modularev/Nemesis/software/examples/polysynth/include/SourceCodeProItalic14.h

const uint8_t SourceCodePro_ExtraLightItalic14pt7bBitmaps[] PROGMEM = {
  0x04, 0x20, 0x82, 0x08, 0x21, 0x04, 0x10, 0x41, 0x08, 0x00, 0x00, 0x18,
  0xE3, 0x80, 0x61, 0xB0, 0xD8, 0x68, 0x24, 0x12, 0x0A, 0x09, 0x04, 0x02,
  0x10, 0x10, 0x81, 0x04, 0x08, 0x40, 0x42, 0x1F, 0xDC, 0x21, 0x01, 0x08,
  0x10, 0x40, 0x84, 0x04, 0x21, 0xFF, 0xC2, 0x10, 0x10, 0x81, 0x04, 0x08,
  0x40, 0x42, 0x02, 0x10, 0x00, 0x00, 0x80, 0x08, 0x00, 0x80, 0x10, 0x0F,
  0x81, 0x06, 0x20, 0x12, 0x00, 0x20, 0x01, 0x00, 0x08, 0x00, 0x60, 0x01,
  0x80, 0x04, 0x00, 0x20, 0x02, 0x00, 0x28, 0x02, 0x40, 0x43, 0xF8, 0x08,
  0x00, 0x80, 0x08, 0x00, 0x80, 0x18, 0x00, 0x33, 0x00, 0x50, 0x80, 0x50,
  0x40, 0x48, 0x20, 0x44, 0x10, 0x42, 0x08, 0x41, 0x08, 0x00, 0x78, 0x00,
  0x00, 0x0C, 0x00, 0x19, 0x80, 0x88, 0x40, 0x88, 0x20, 0x84, 0x10, 0x82,
  0x08, 0x81, 0x04, 0x80, 0x84, 0x00, 0x3C, 0x00, 0x03, 0xC0, 0x10, 0x80,
  0x42, 0x02, 0x08, 0x08, 0x40, 0x22, 0x00, 0x90, 0x01, 0x80, 0x0C, 0x00,
  0x50, 0x16, 0x20, 0x50, 0x82, 0x81, 0x12, 0x04, 0x48, 0x0A, 0x20, 0x10,
  0x81, 0xA1, 0xF8, 0x60, 0x6D, 0xA4, 0xA4, 0x00, 0xC0, 0x40, 0x20, 0x10,
  0x08, 0x04, 0x02, 0x00, 0x80, 0x40, 0x10, 0x08, 0x02, 0x00, 0x80, 0x20,
  0x08, 0x02, 0x00, 0x80, 0x20, 0x08, 0x01, 0x00, 0x40, 0x10, 0x02, 0x00,
  0x40, 0x08, 0x00, 0x04, 0x01, 0x00, 0x20, 0x04, 0x01, 0x00, 0x20, 0x08,
  0x02, 0x00, 0x80, 0x10, 0x04, 0x02, 0x00, 0x80, 0x20, 0x08, 0x02, 0x01,
  0x00, 0x40, 0x20, 0x08, 0x04, 0x02, 0x01, 0x01, 0x80, 0x80, 0x00, 0x02,
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
  {   920,  14,  18,  16,    2,  -17 },   // 0x47 'G'
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

const GFXfont SourceCodePro_ExtraLightItalic14pt7b PROGMEM = {
  (uint8_t  *)SourceCodePro_ExtraLightItalic14pt7bBitmaps,
  (GFXglyph *)SourceCodePro_ExtraLightItalic14pt7bGlyphs,
  0x20, 0x7E, 34 };

// Approx. 3130 bytes
