modularev/Nemesis/software/examples/polysynth/include/SourceCodePro6.h

const uint8_t SourceCodePro_ExtraLight6pt7bBitmaps[] PROGMEM = {
  0xF9, 0xB6, 0x80, 0x4A, 0xBE, 0xA5, 0x7D, 0x4A, 0x21, 0x17, 0x06, 0x08,
  0x31, 0x71, 0x00, 0x43, 0x4A, 0xA7, 0x00, 0x45, 0x52, 0xC7, 0x62, 0x46,
  0x10, 0xC6, 0xA9, 0x3F, 0xE0, 0x2A, 0x49, 0x24, 0x88, 0x80, 0x88, 0x92,
  0x49, 0x2A, 0x00, 0x27, 0xC8, 0xA0, 0x21, 0x3E, 0x42, 0x00, 0x5C, 0x80,
  0x08, 0x84, 0x42, 0x11, 0x08, 0x44, 0x00, 0x74, 0x63, 0x5A, 0xC6, 0x2E,
  0x23, 0x08, 0x42, 0x10, 0x9F, 0x74, 0x42, 0x11, 0x11, 0x1F, 0x74, 0x42,
  0x27, 0x04, 0x3F, 0x10, 0x8C, 0xA9, 0x7C, 0x42, 0x7C, 0x21, 0xE0, 0x84,
  0x3E, 0x3A, 0x21, 0xE8, 0xC6, 0x2F, 0xF8, 0x44, 0x22, 0x10, 0x84, 0x74,
  0x62, 0x9B, 0x46, 0x3F, 0x74, 0x63, 0x17, 0x84, 0x3E, 0x84, 0x40, 0x17,
  0x19, 0x11, 0x82, 0x0C, 0xFF, 0xC0, 0xC1, 0x04, 0x32, 0x60, 0xF1, 0x11,
  0x20, 0x02, 0x7C, 0x67, 0x5C, 0xDE, 0x10, 0x78, 0x21, 0x14, 0xA4, 0xDE,
  0x31, 0xF4, 0x63, 0xE8, 0xC6, 0x3F, 0x7C, 0x21, 0x08, 0x42, 0x0F, 0xF4,
  0x63, 0x18, 0xC6, 0x3E, 0xF8, 0x8E, 0x88, 0x8F, 0xF8, 0x88, 0xF8, 0x88,
  0x7C, 0x21, 0x09, 0xC6, 0x2F, 0x8C, 0x63, 0xF8, 0xC6, 0x31, 0xF9, 0x08,
  0x42, 0x10, 0x9F, 0x78, 0x42, 0x10, 0x84, 0x3E, 0x8A, 0x49, 0x28, 0xD2,
  0x48, 0xA1, 0x88, 0x88, 0x88, 0x8F, 0x8C, 0x67, 0xBD, 0xD6, 0x31, 0x8C,
  0x73, 0x5A, 0xCE, 0x71, 0x74, 0x63, 0x18, 0xC6, 0x2E, 0xF4, 0x63, 0x1F,
  0x42, 0x10, 0x74, 0x63, 0x18, 0xC6, 0x2A, 0x20, 0xC0, 0xF4, 0x63, 0x1F,
  0x4A, 0x31, 0x7C, 0x20, 0xC1, 0x04, 0x3F, 0xF9, 0x08, 0x42, 0x10, 0x84,
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
  {   156,   5,   8,   7,    1,   -7 },   // 0x47 'G'
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

const GFXfont SourceCodePro_ExtraLight6pt7b PROGMEM = {
  (uint8_t  *)SourceCodePro_ExtraLight6pt7bBitmaps,
  (GFXglyph *)SourceCodePro_ExtraLight6pt7bGlyphs,
  0x20, 0x7E, 15 };

// Approx. 1090 bytes
